george-ags/lm-bbw/tray-models/photos/flush2.jpeg

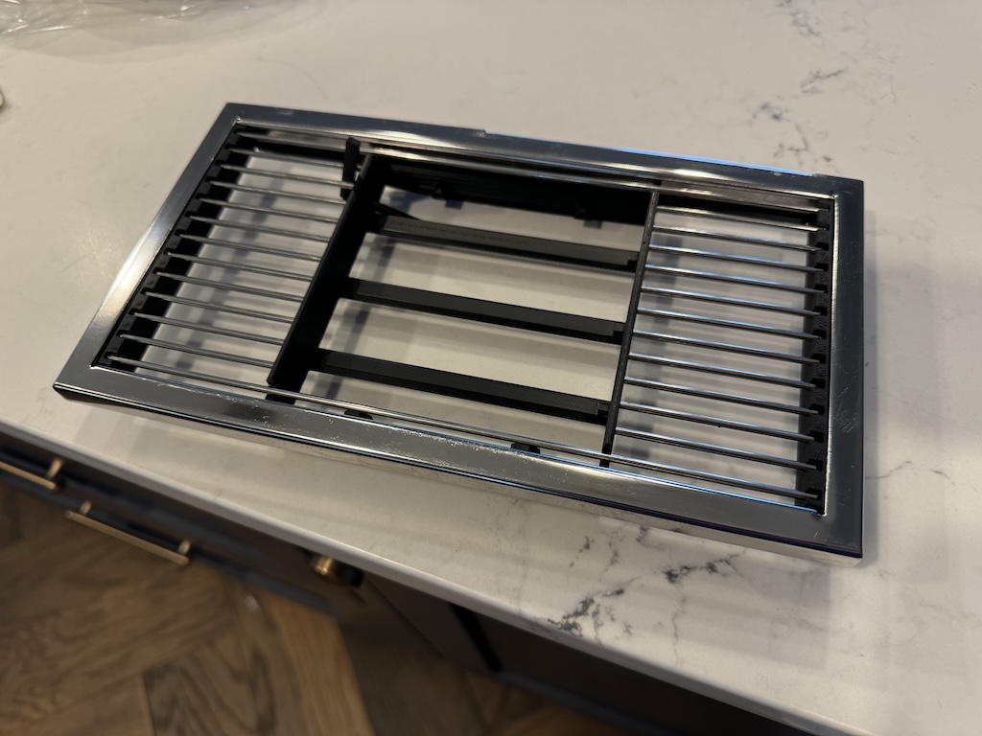
tray-models/photos/flush2.jpeg
